KUHLwasStolen/E92dashModEnder3Display/schematic/ReceiverSchematic/ReceiverSchematic.kicad_sch

## KiCad design schematic/ReceiverSchematic/ReceiverSchematic.kicad_sch (2025-03-14, an earlier design)

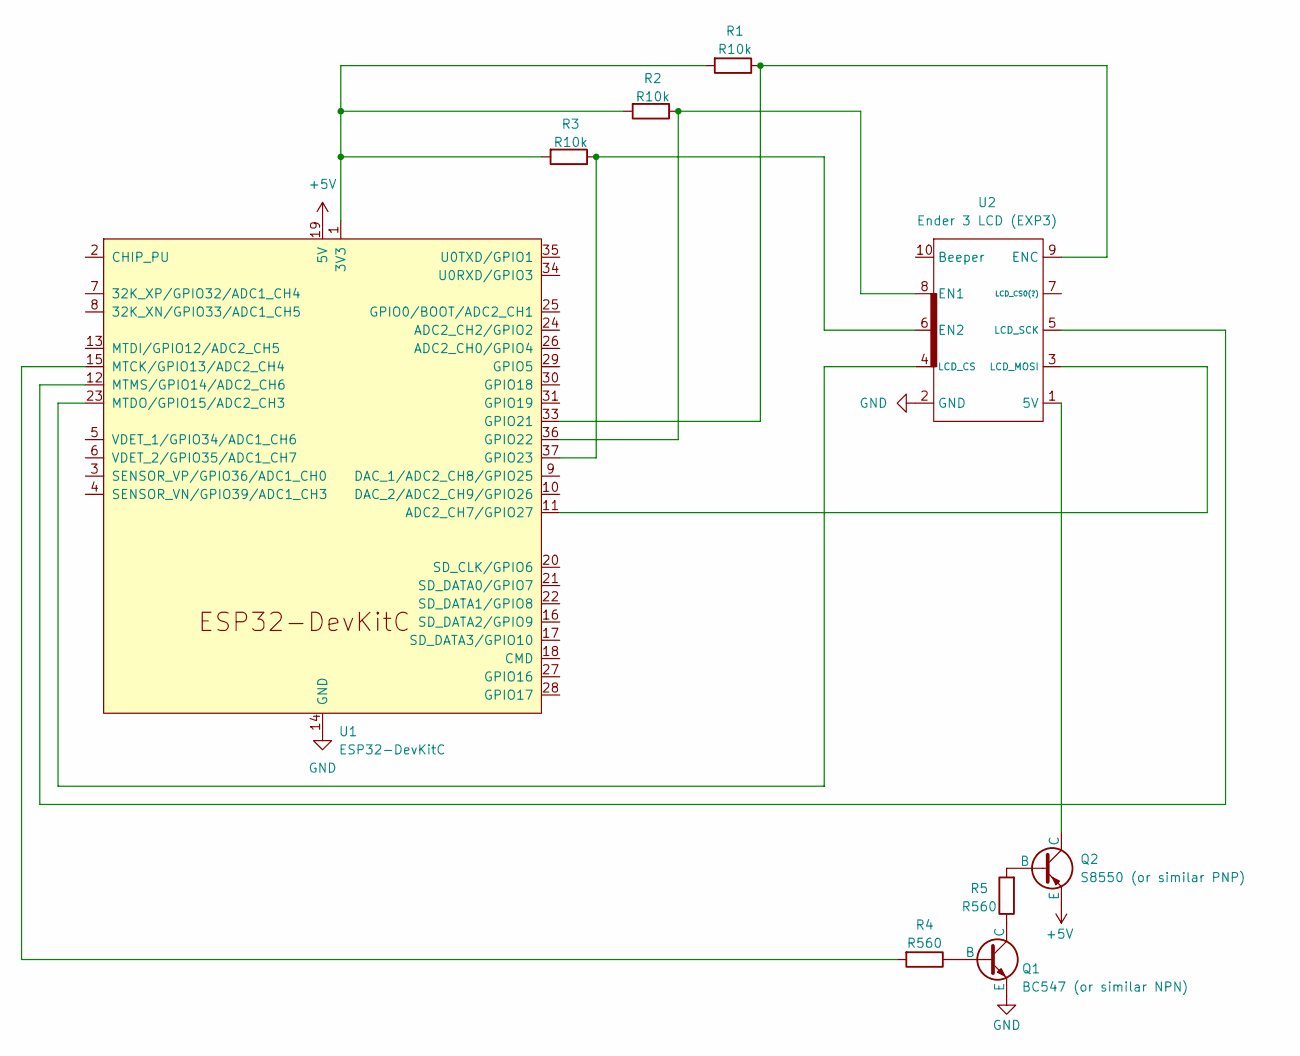
[picture p18: schematic ReceiverSchematic.kicad_sch]

Parts:
Q1: BC547 (or similar NPN); TO-92_Inline
Q2: S8550 (or similar PNP); TO-92_Inline
R1, R2, R3: R10k
R4, R5: R560
U1: ESP32-DevKitC
U2: Ender 3 LCD (EXP3)

Connections:
+5V: Q2.1 (E), U1.19 (5V)
GND: Q1.3 (E), U1.14 (GND), U1.32 (GND), U1.38 (GND), U2.2 (GND)
unnamed: Q1.1 (C), R5.1
unnamed: Q1.2 (B), R4.1
unnamed: Q2.2 (B), R5.2
unnamed: Q2.3 (C), U2.1 (5V)
unnamed: R1.1, U1.33 (GPIO21), U2.9 (ENC)
unnamed: R1.2, R2.2, R3.2, U1.1 (3V3)
unnamed: R2.1, U1.36 (GPIO22), U2.8 (EN1)
unnamed: R3.1, U1.37 (GPIO23), U2.6 (EN2)
unnamed: R4.2, U1.15 (MTCK/GPIO13/ADC2_CH4)
unnamed: U1.11 (ADC2_CH7/GPIO27), U2.3 (LCD_MOSI)
unnamed: U1.12 (MTMS/GPIO14/ADC2_CH6), U2.5 (LCD_SCK)
unnamed: U1.23 (MTDO/GPIO15/ADC2_CH3), U2.4 (LCD_CS)
