KUHLwasStolen/E92dashModEnder3Display/schematic/SenderSchematic/SenderSchematic.kicad_sch

## KiCad design schematic/SenderSchematic/SenderSchematic.kicad_sch (2025-02-21)

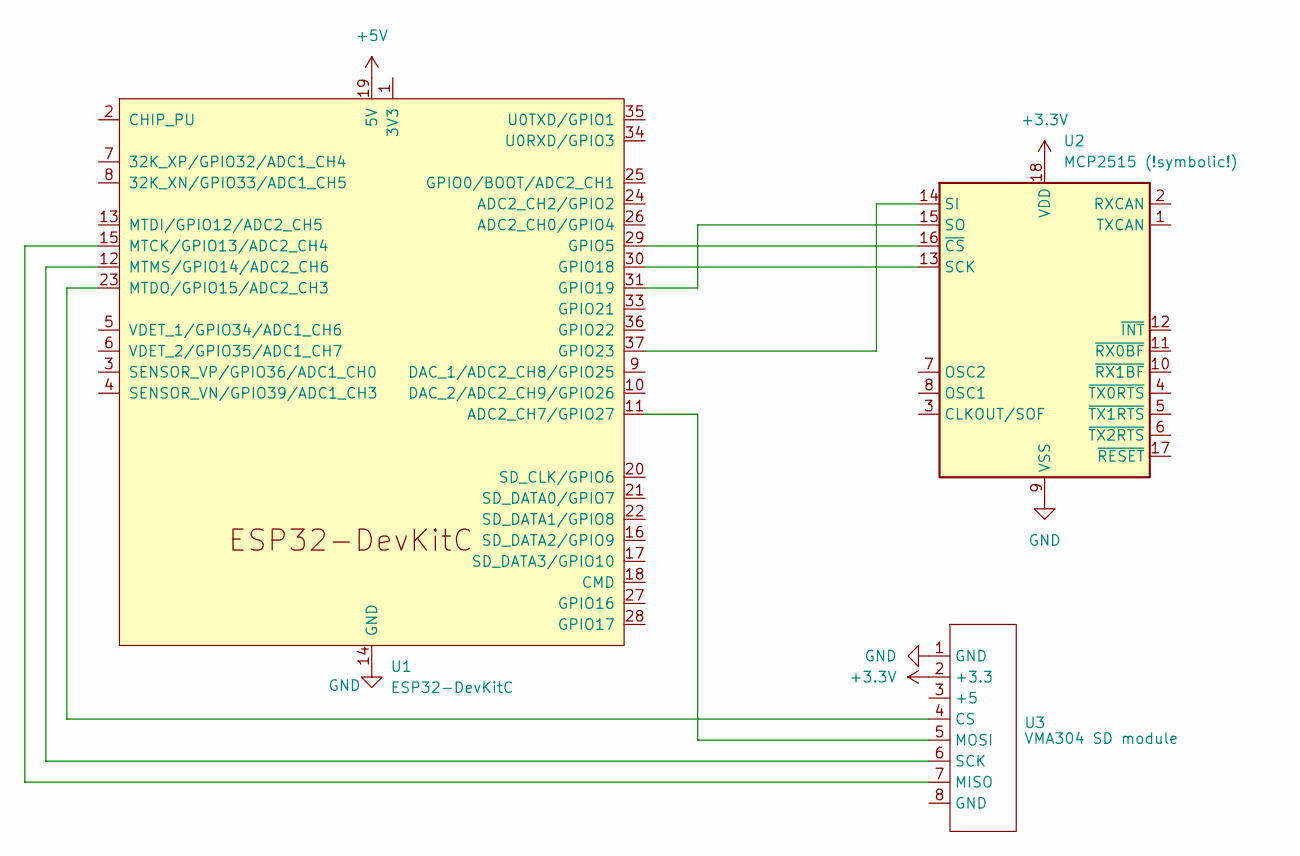
[picture p19: schematic SenderSchematic.kicad_sch]

Parts:
U1: ESP32-DevKitC
U2: MCP2515 (!symbolic!); SOIC-18W_7.5x11.6mm_P1.27mm
U3: VMA304 SD module

Connections:
+3.3V: U2.18 (VDD), U3.2 (+3.3)
+5V: U1.19 (5V)
GND: U1.14 (GND), U1.32 (GND), U1.38 (GND), U2.9 (VSS), U3.1 (GND)
unnamed: U1.11 (ADC2_CH7/GPIO27), U3.5 (MOSI)
unnamed: U1.12 (MTMS/GPIO14/ADC2_CH6), U3.6 (SCK)
unnamed: U1.15 (MTCK/GPIO13/ADC2_CH4), U3.7 (MISO)
unnamed: U1.23 (MTDO/GPIO15/ADC2_CH3), U3.4 (CS)
unnamed: U1.29 (GPIO5), U2.16 (~CS)
unnamed: U1.30 (GPIO18), U2.13 (SCK)
unnamed: U1.31 (GPIO19), U2.15 (SO)
unnamed: U1.37 (GPIO23), U2.14 (SI)
