KUHLwasStolen/E92dashModEnder3Display/schematic/e92dashModSchematic/e92dashModSchematic.kicad_sch

## KiCad design schematic/e92dashModSchematic/e92dashModSchematic.kicad_sch (2025-01-24)

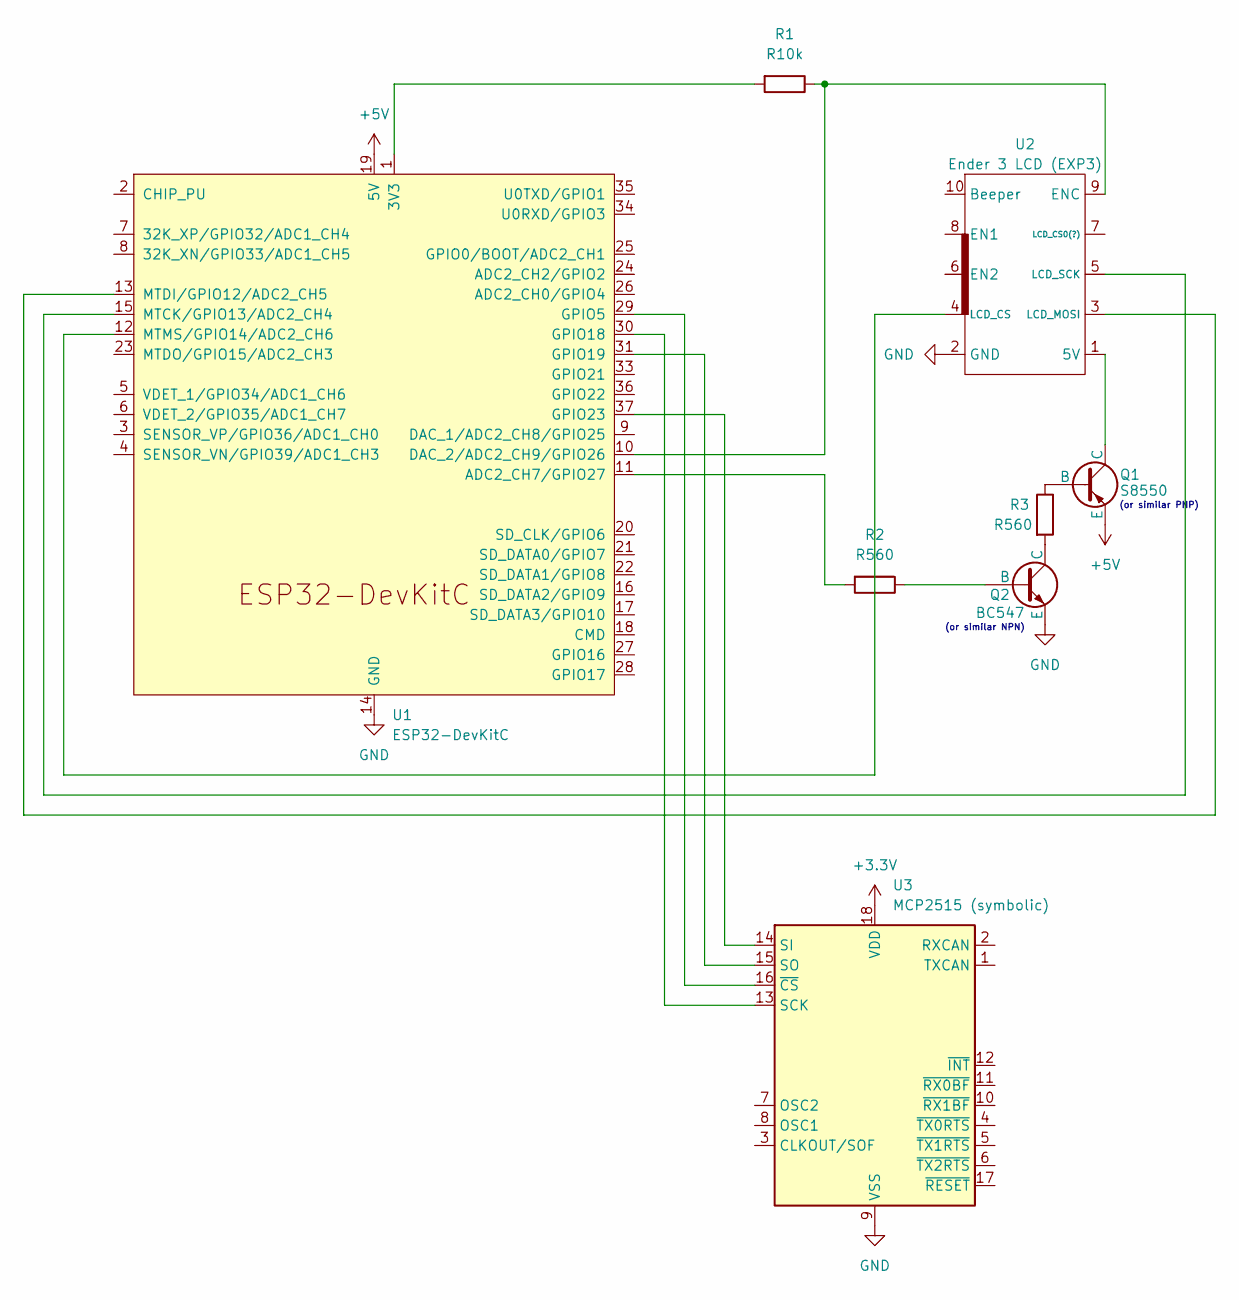
[picture p20: schematic e92dashModSchematic.kicad_sch]

Parts:
Q1: S8550; TO-92_Inline
Q2: BC547; TO-92_Inline
R1: R10k
R2, R3: R560
U1: ESP32-DevKitC
U2: Ender 3 LCD (EXP3)
U3: MCP2515 (symbolic); SOIC-18W_7.5x11.6mm_P1.27mm

Connections:
+3.3V: U3.18 (VDD)
+5V: Q1.1 (E), U1.19 (5V)
GND: Q2.3 (E), U1.14 (GND), U1.32 (GND), U1.38 (GND), U2.2 (GND), U3.9 (VSS)
unnamed: Q1.2 (B), R3.1
unnamed: Q1.3 (C), U2.1 (5V)
unnamed: Q2.1 (C), R3.2
unnamed: Q2.2 (B), R2.1
unnamed: R1.1, U1.10 (DAC_2/ADC2_CH9/GPIO26), U2.9 (ENC)
unnamed: R1.2, U1.1 (3V3)
unnamed: R2.2, U1.11 (ADC2_CH7/GPIO27)
unnamed: U1.12 (MTMS/GPIO14/ADC2_CH6), U2.4 (LCD_CS)
unnamed: U1.13 (MTDI/GPIO12/ADC2_CH5), U2.3 (LCD_MOSI)
unnamed: U1.15 (MTCK/GPIO13/ADC2_CH4), U2.5 (LCD_SCK)
unnamed: U1.29 (GPIO5), U3.16 (~CS)
unnamed: U1.30 (GPIO18), U3.13 (SCK)
unnamed: U1.31 (GPIO19), U3.15 (SO)
unnamed: U1.37 (GPIO23), U3.14 (SI)

Notes on the sheet:
(or similar NPN)
(or similar PNP)
